usr-ein/TriMixxx/prolinks-compat/research/10-mixxx-prolink-implementation-plan.md

# 10 — Implementation plan: two-way ProLink in Mixxx

The approved build plan for Phase B. Supersedes the sketch in
[08-python-poc-plan.md](08-python-poc-plan.md) and corrects the licensing claims in
[09-mixxx-integration-notes.md](09-mixxx-integration-notes.md).

Grounded in a full read of the Mixxx source at `../mixxx` (fork of 2.5.6). Line
references are to that tree.

**Revised 2026-07-30** for two changes of direction:

1. **Serving is v1 scope, not a later phase.** Phase A proved both directions
   against real hardware, so the old "consume now, serve someday" split has no
   remaining justification. Former Phase C is folded into Phase B.
2. **Kaitai Struct describes the wire formats.** With one large caveat that
   shapes the whole design — see [§Kaitai](#kaitai-struct-what-it-can-and-cannot-do-here).

> Implement from [`docs/PROTOCOL.md`](../docs/PROTOCOL.md), not from this file
> and not from `research/00`–`09`. This document says *how to build it in Mixxx*;
> PROTOCOL.md says *what the bytes are*. Where they disagree, PROTOCOL.md wins.

**Status, 2026-07-31 — the serve side is built and verified on hardware.** Two
CDJ-2000NXS browse and play from sticks in the deck's own USB ports: media query
answered, portmapper and mountd and nfsd bound, dbserver on 1051, both slots
advertised (`/C/` USB and `/B/` SD) with their real labels and counts. Yanking a
stick mid-play stops the playing deck cleanly and clears the slot within ~2 s;
re-inserting restores it to the same slot. What that leaves untested is the
long tail rather than the mechanism: mixers, CDJ-3000s, more than two peers, and
a set's worth of uptime. Findings from the exercise are `F52` onward.

## Working-directory conventions

- `prolinks-compat/` — research docs, the Python PoC (`prolinks_poc/`, `tests/`),
  and the `.ksy` sources. `captures/` and `research/ref-repos/` stay git-ignored.
- `mixxx/` — the C++ fork. No PoC artifacts land there; only `src/`, `res/`,
  `CMakeLists.txt` changes, plus the generated Kaitai output.
- Commit straight to `main` in both repos — no PRs (standing convention for this
  project). Upstreaming to mixxxdj/mixxx is a separate, later exercise; see
  [§Upstreaming](#upstreaming-reality-check).

---

## Target behaviour

The feature as specified, in the order a user meets it.

### On boot

- If **enabled in Mixxx settings** (default off), Mixxx acts as a CDJ on the
  Pro DJ Link network. Disabled, it transmits nothing and binds nothing.
- It advertises a **given player number, or AUTO** — AUTO is the default.
- It watches the filesystem for mounted volumes carrying a rekordbox database,
  and **reports media inserted/ejected** to other players as it sees them appear
  and disappear.

### Serving

- Other CDJs **browse the media mounted in Mixxx** — the same categories, sorts,
  drill-downs and search a real CDJ offers — and load and play tracks from them.
- **Only the first two volumes** are served: the first fills the **USB** slot,
  the second the **SD** slot. A third is ignored.
- **The internal Mixxx library is never shared.** Only rekordbox media are.

### Consuming

- Mixxx finds other CDJs on the network and lists them in the library sidebar
  under **ProLink**:

  ```
  ProLink
  ├─ 1 · CDJ-2000nexus
  │  ├─ USB
  │  └─ SD
  └─ 2 · CDJ-2000nexus  (offline)
  ```

- Opening a slot **downloads and parses that medium's `export.pdb`** over NFS.
- Loading a track **downloads the whole file into a local cache**, which is
  **cleared at every boot**.

> **Reading of "menu bar".** The requirement says CDJs "display in the menu bar
> under ProLink", with the path `ProLink > 1 - CDJ 2000 Nxs > USB/SD`. A
> three-level browsable, track-loadable hierarchy is the library sidebar, not
> Qt's menu bar — Mixxx has no other surface that can do this. Built as a
> `LibraryFeature`.
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
