usr-ein/TriMixxx/boards/one_button/v1_layout.png

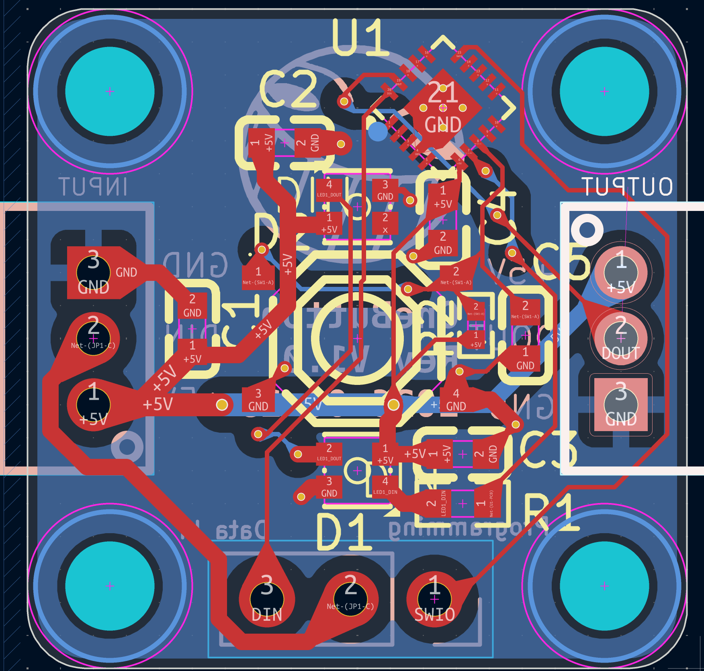
boards/one_button/v1_layout.png
