usr-ein/TriMixxx/handmade_pcb/export_kicad10_b_cu.png

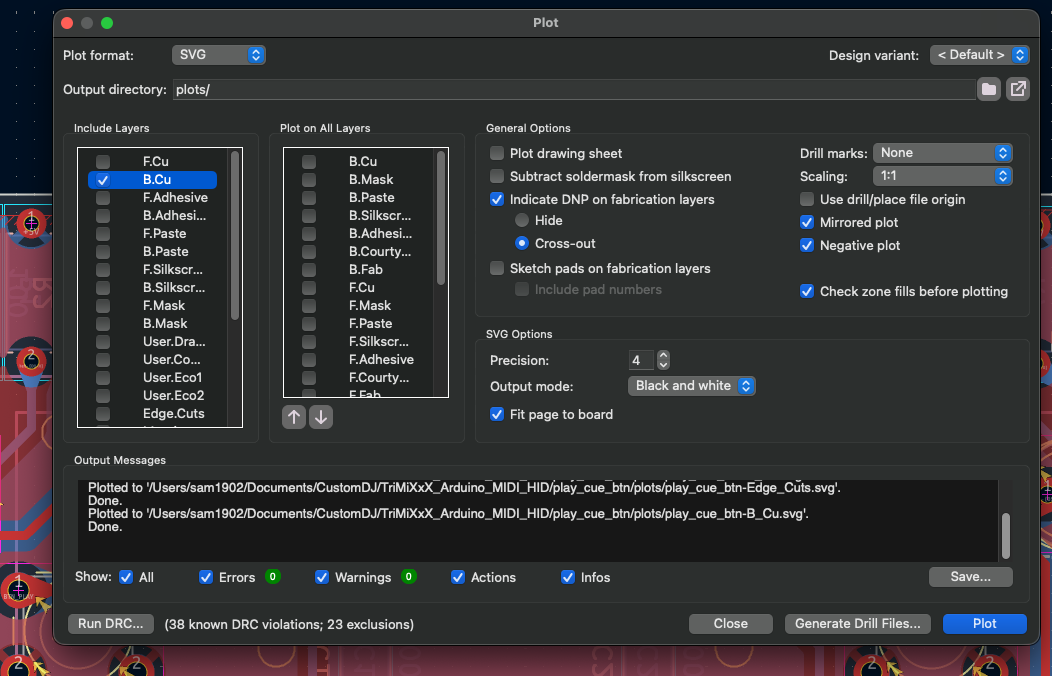
handmade_pcb/export_kicad10_b_cu.png
