usr-ein/TriMixxx/ref_sizes/cdj1000mk3_top_case_skwik.png

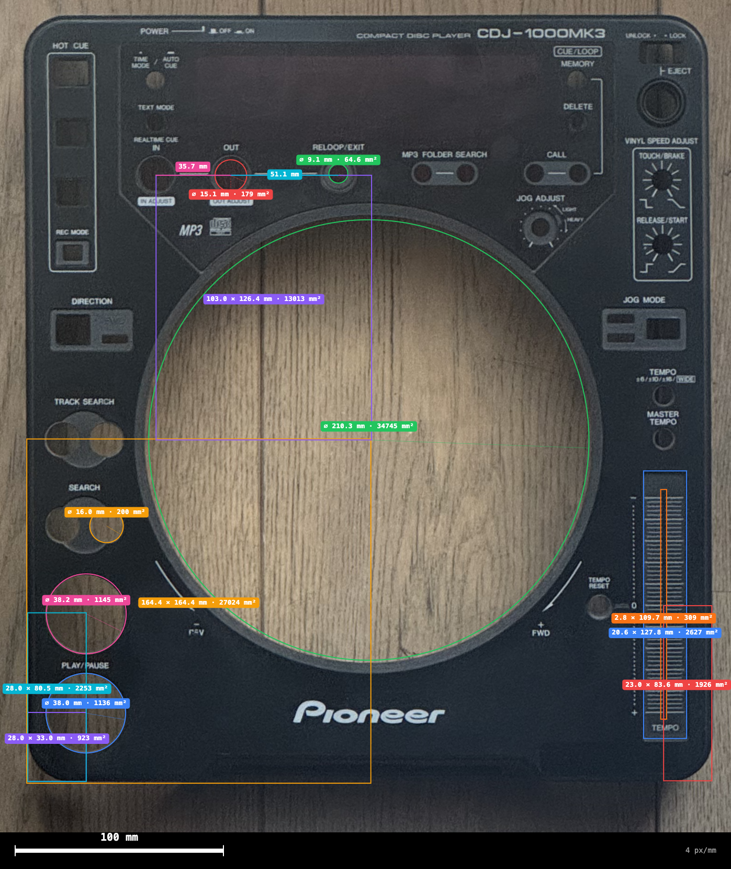
ref_sizes/cdj1000mk3_top_case_skwik.png
