usr-ein/TriMixxx/ref_sizes/cdj2000nx2-skwik.png

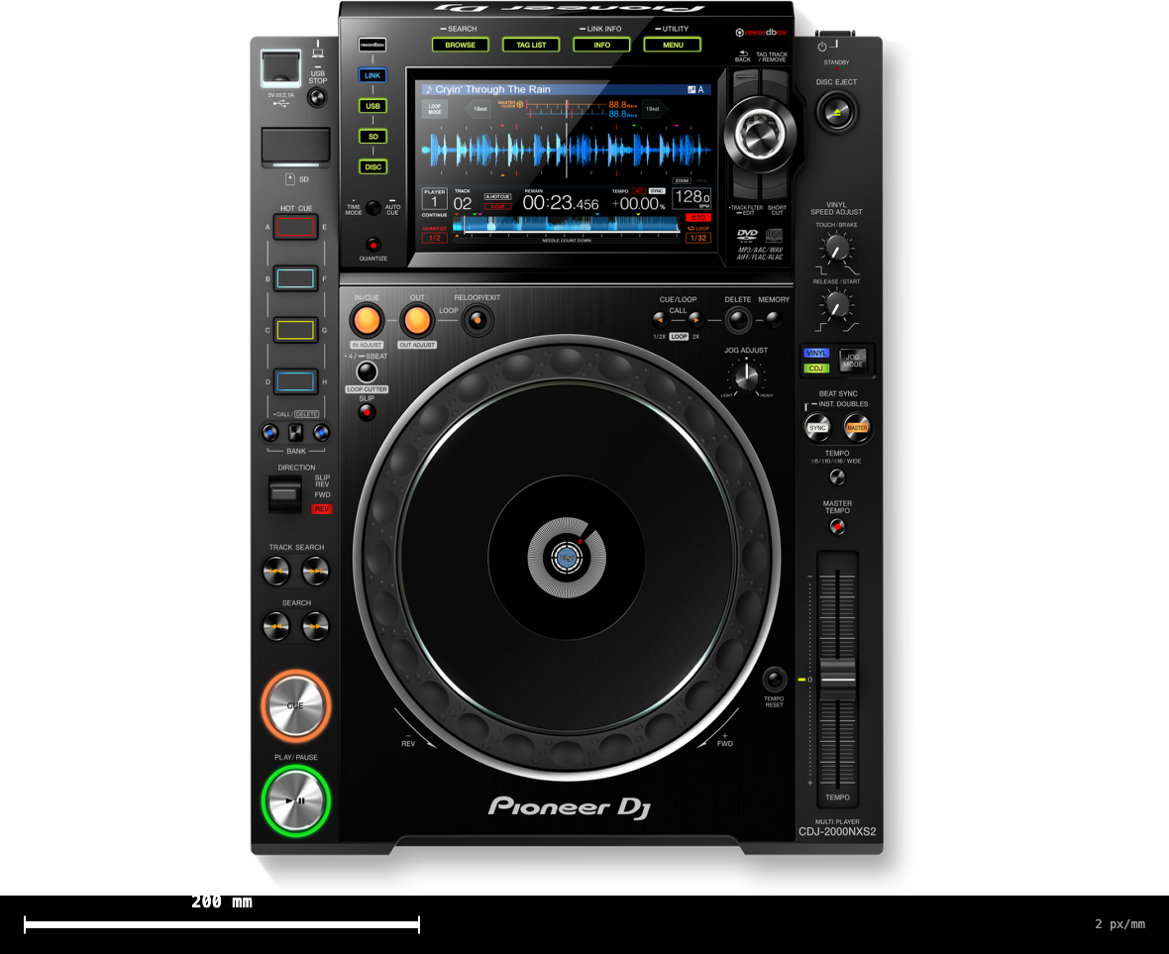
ref_sizes/cdj2000nx2-skwik.png
