usr-ein/TriMixxx/ref_sizes/cdj2000nx2.png

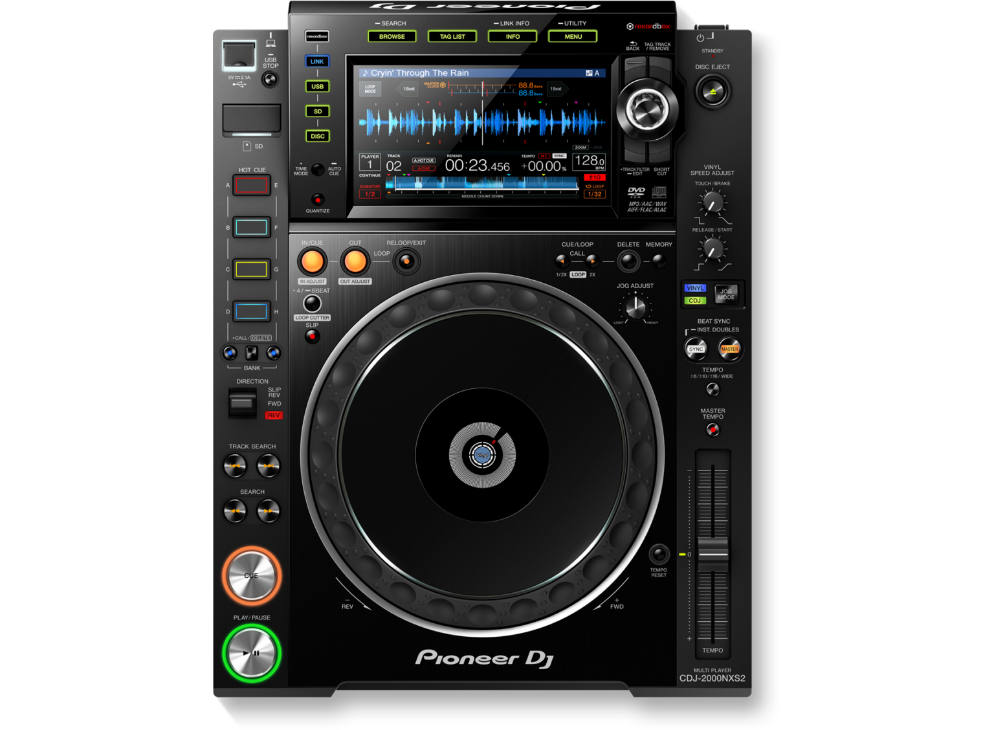
ref_sizes/cdj2000nx2.png
