usr-ein/TriMixxx/ref_sizes/cdj3000-skwik.png

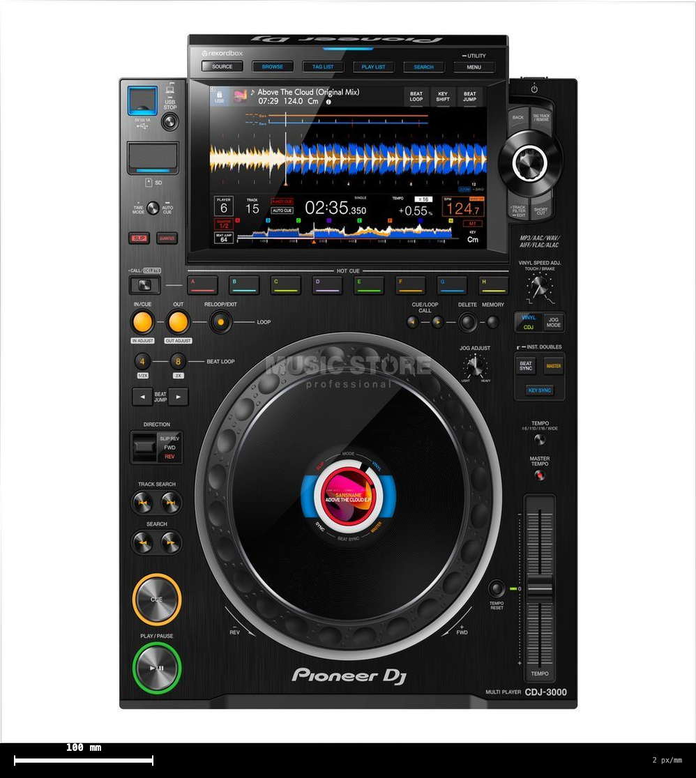
ref_sizes/cdj3000-skwik.png
