usr-ein/TriMixxx/ref_sizes/CDJ-3000_top.png

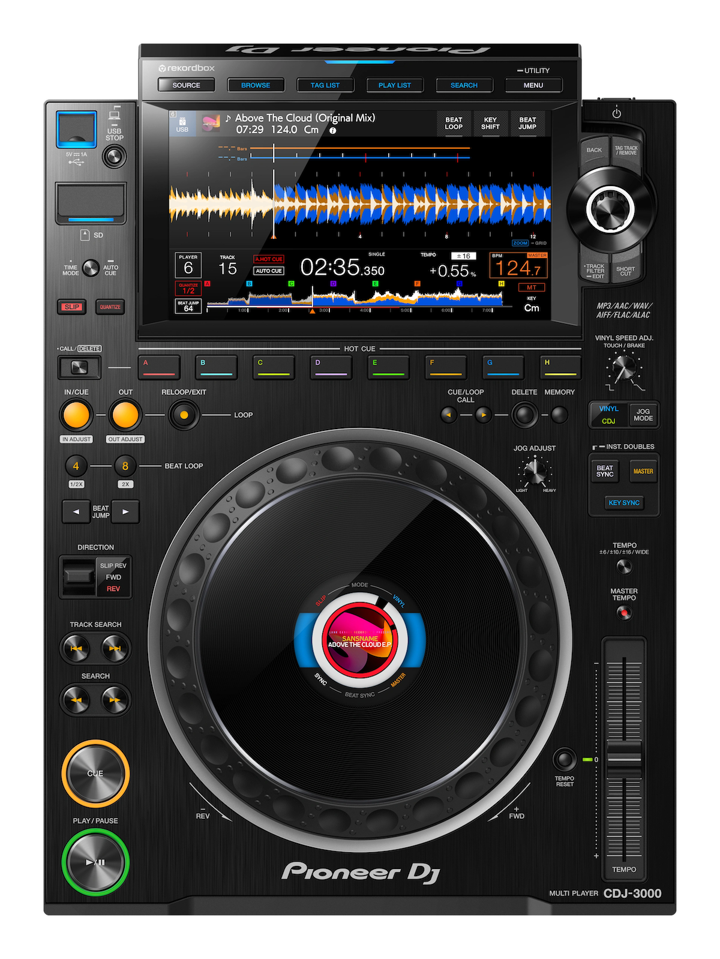
ref_sizes/CDJ-3000_top.png
