usr-ein/TriMixxx/ref_sizes/mixxx.png

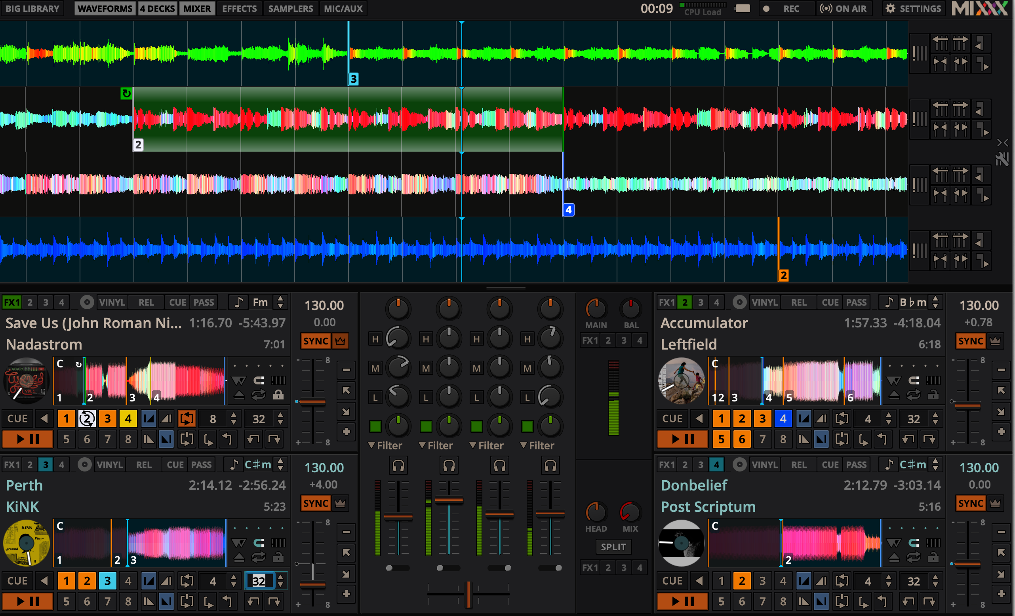
ref_sizes/mixxx.png
