usr-ein/TriMixxx/ref_sizes/scr_image.png

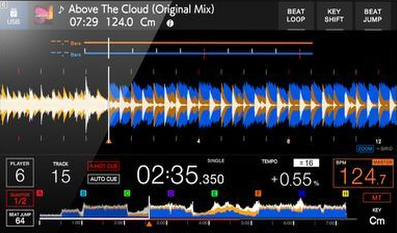
ref_sizes/scr_image.png
