usr-ein/TriMixxx/screenshots/audio_2026-02-17.png

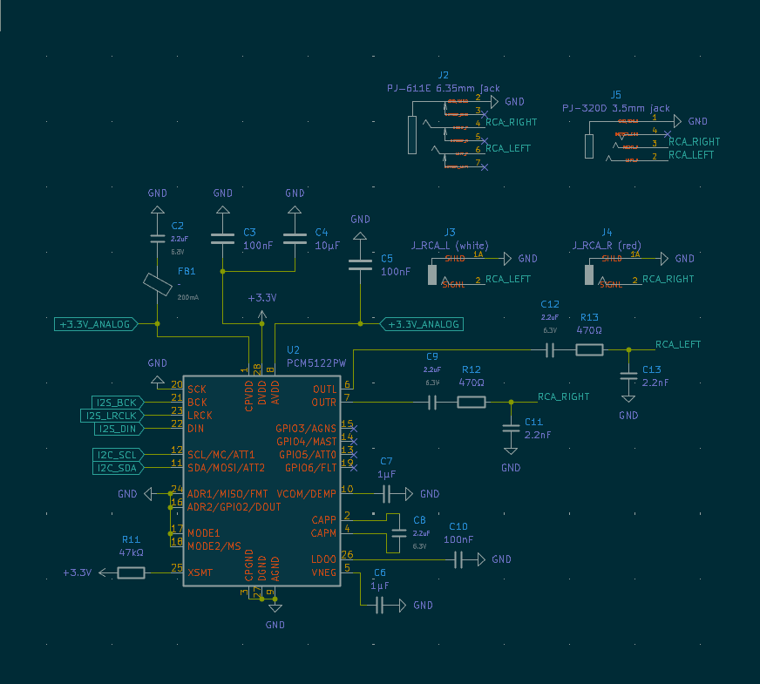
screenshots/audio_2026-02-17.png
