usr-ein/TriMixxx/screenshots/CDJ-MainBoard-v1_fully_routed.png

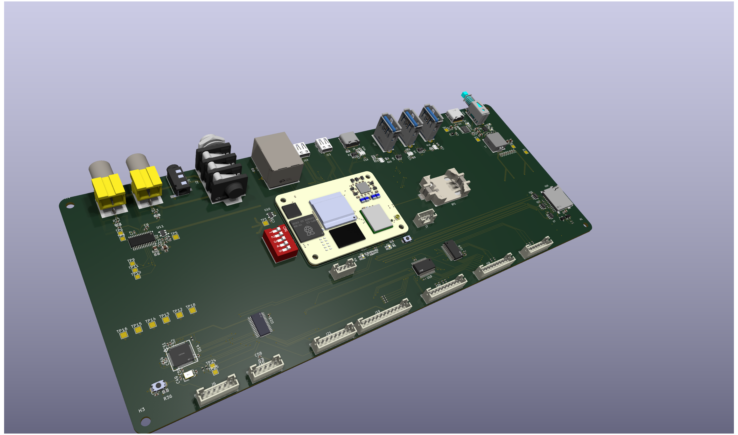
screenshots/CDJ-MainBoard-v1_fully_routed.png
