usr-ein/TriMixxx/screenshots/CDJ-TriMixxx-master-doc_v117_back.png

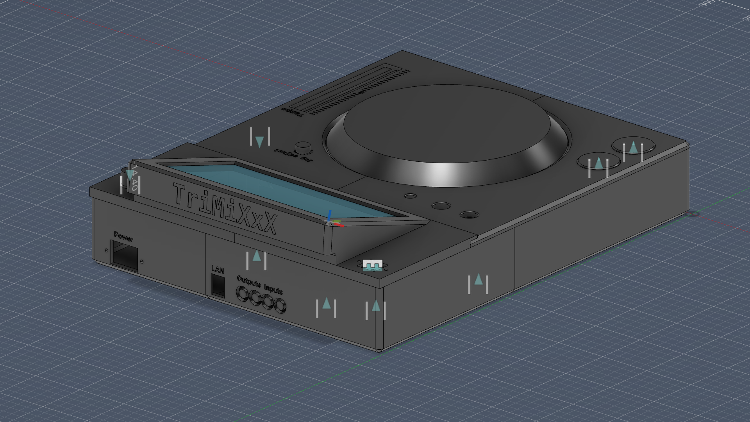
screenshots/CDJ-TriMixxx-master-doc_v117_back.png
