usr-ein/TriMixxx/screenshots/CDJ-TriMixxx-master-doc_v117_front.png

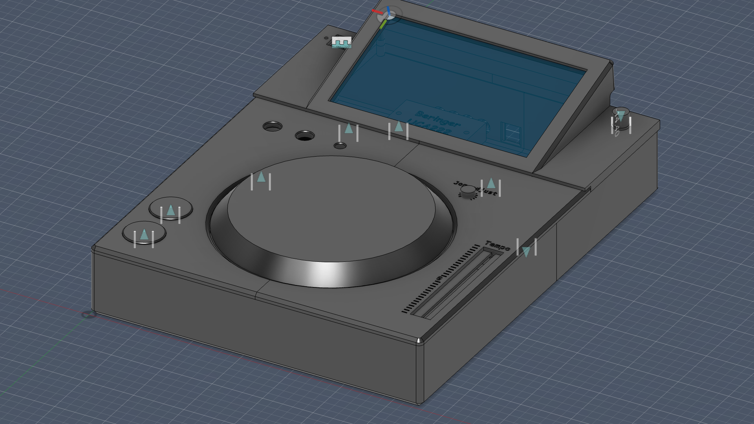
screenshots/CDJ-TriMixxx-master-doc_v117_front.png
