usr-ein/TriMixxx/screenshots/dac_spice.png

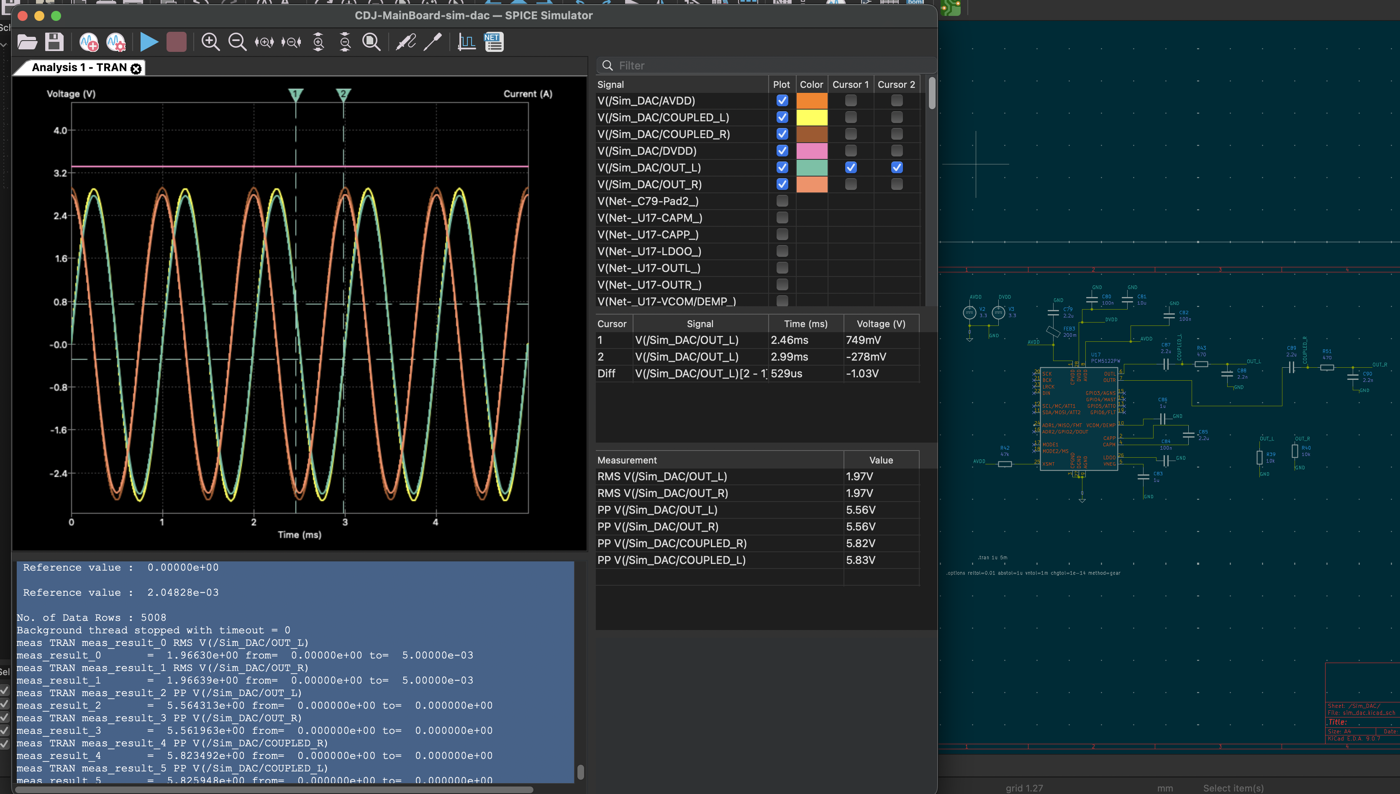
screenshots/dac_spice.png
