usr-ein/TriMixxx/screenshots/midi_arduino_2026-02-17.png

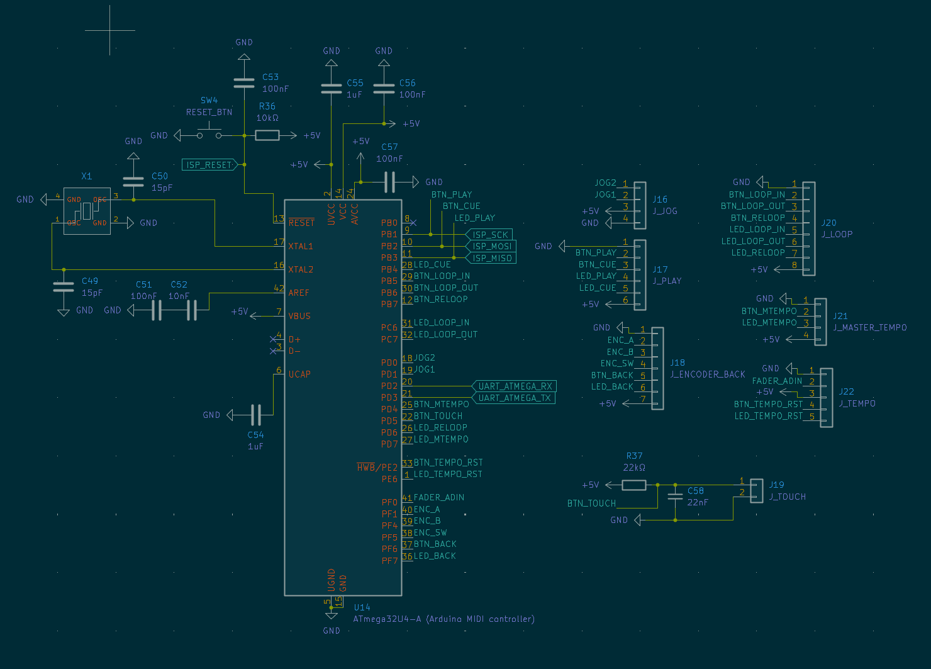
screenshots/midi_arduino_2026-02-17.png
