usr-ein/TriMixxx/screenshots/pcb-3d-render.png

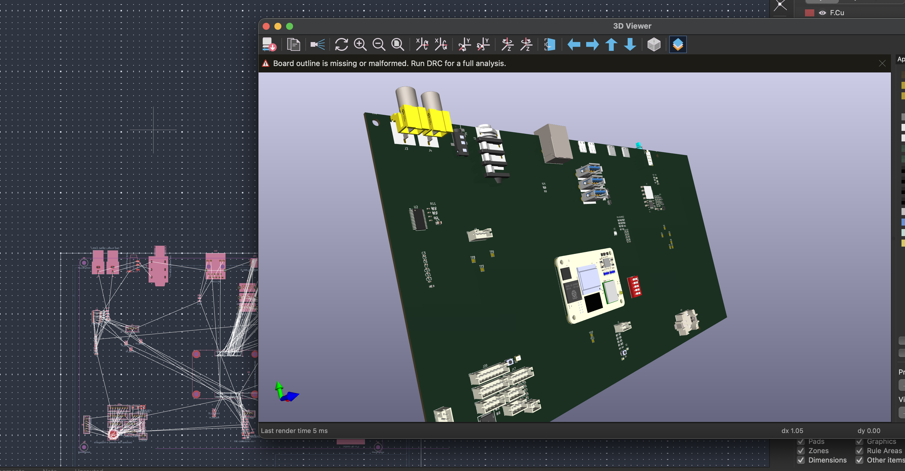
screenshots/pcb-3d-render.png
