usr-ein/TriMixxx/screenshots/power_delivery_2026-02-17.png

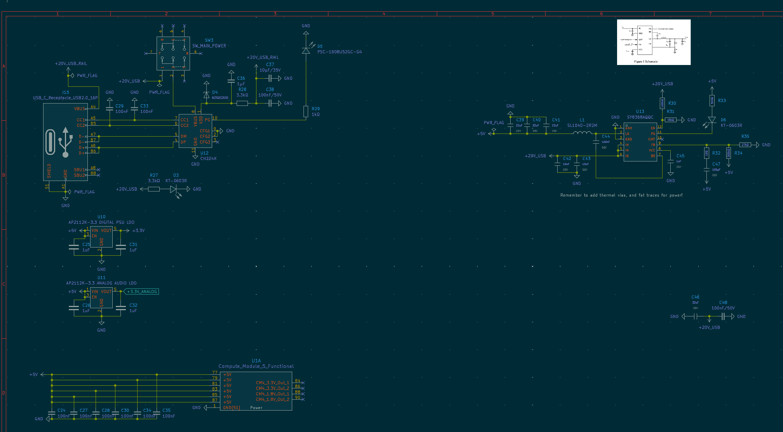
screenshots/power_delivery_2026-02-17.png
