usr-ein/TriMixxx/screenshots/Screenshot 2026-02-08 at 19.56.48.png

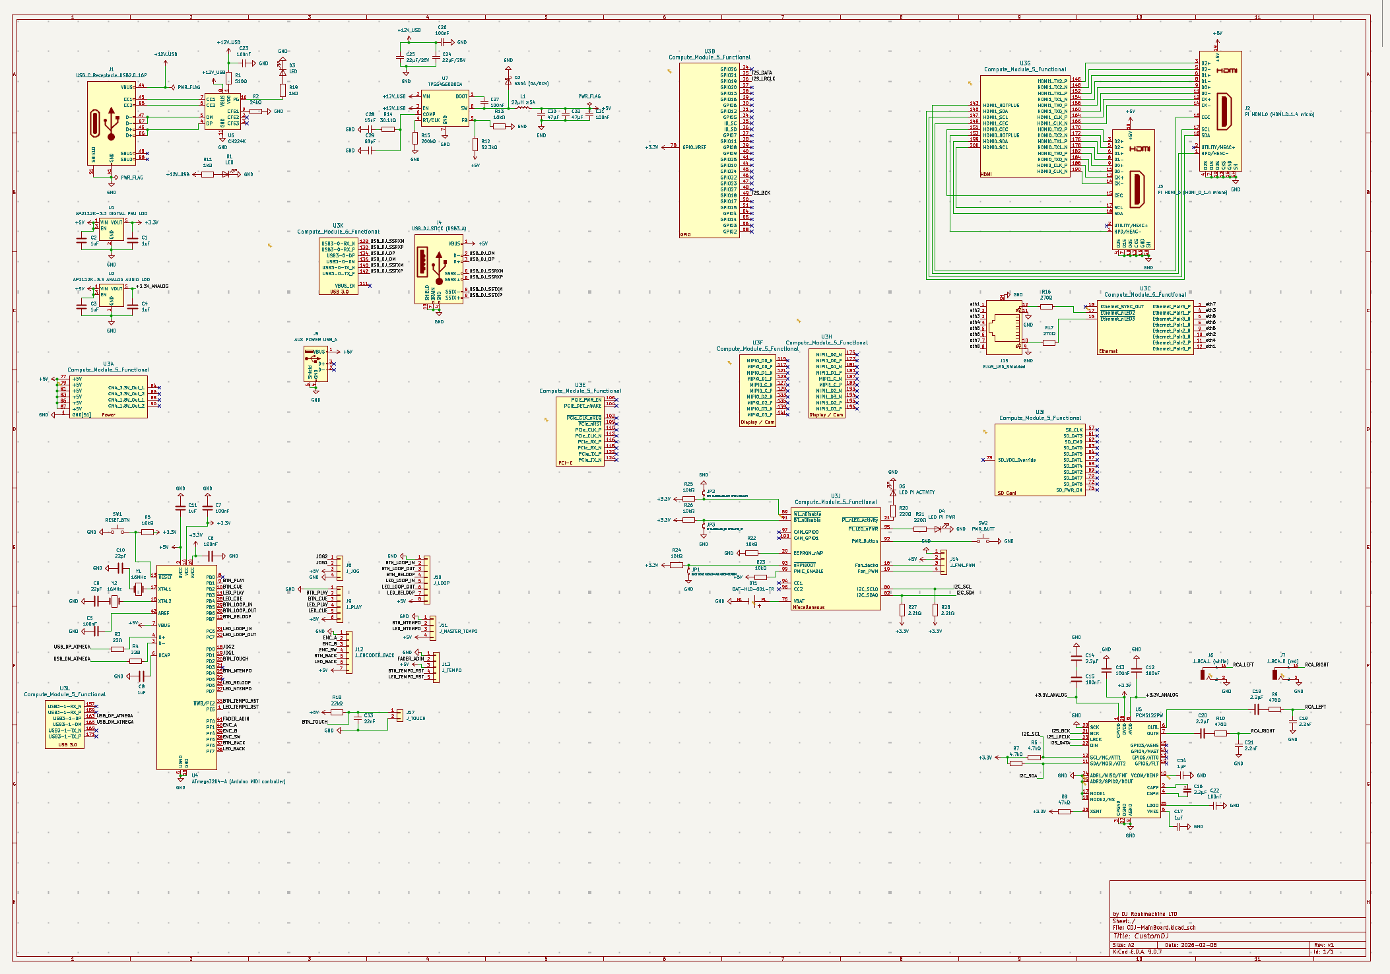
screenshots/Screenshot 2026-02-08 at 19.56.48.png
