usr-ein/TriMixxx/screenshots/usb_2026-02-17.png

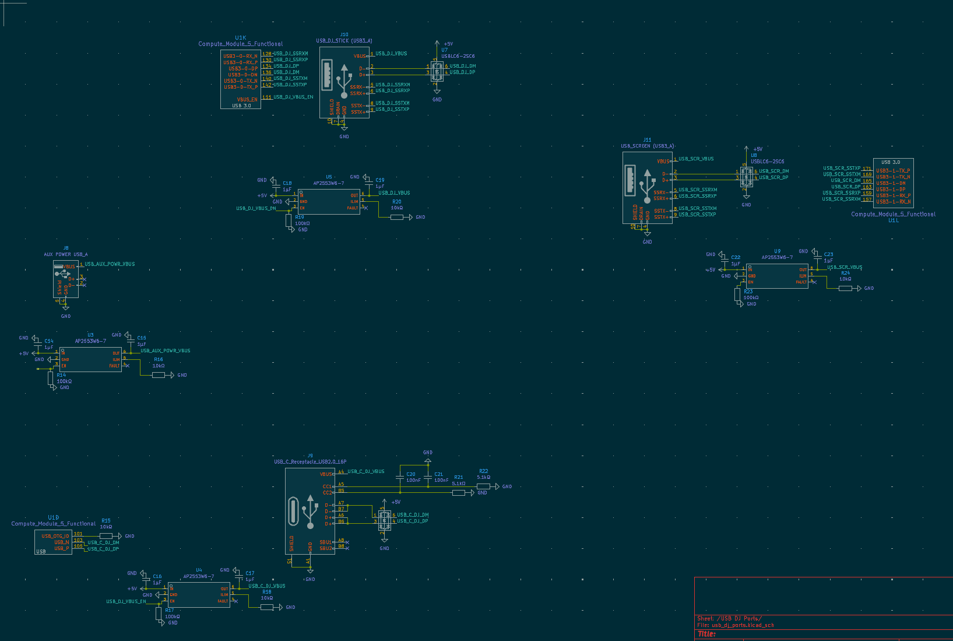
screenshots/usb_2026-02-17.png
