usr-ein/TriMixxx/ref_sizes/IMG_8324-measured-view.png

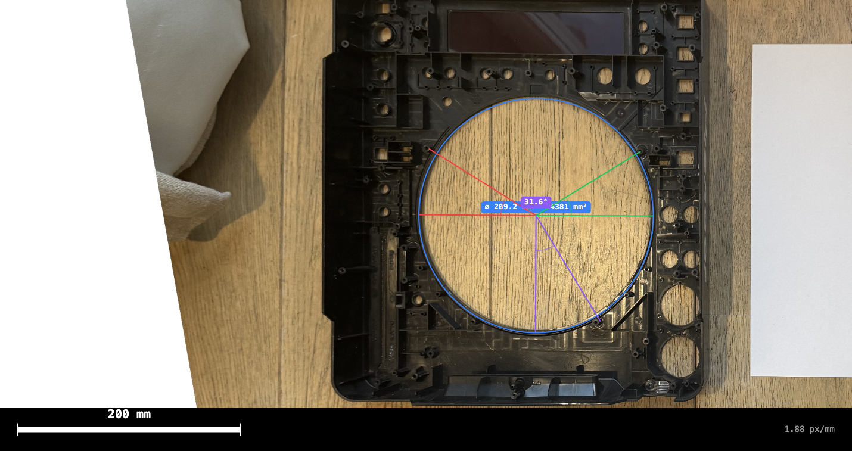
ref_sizes/IMG_8324-measured-view.png
