usr-ein/TriMixxx/ref_sizes/jog_front-measured.png

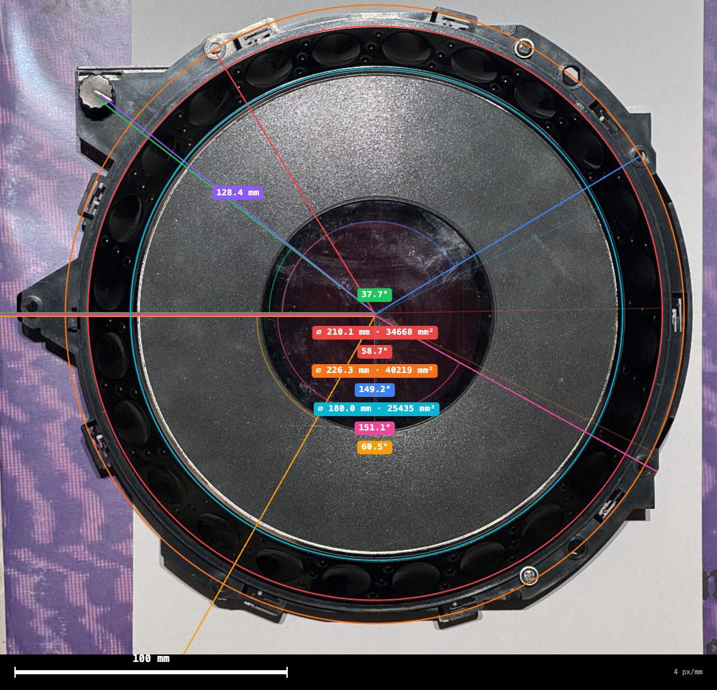
ref_sizes/jog_front-measured.png
