usr-ein/TriMixxx/ref_sizes/jog_side_2-measured.png

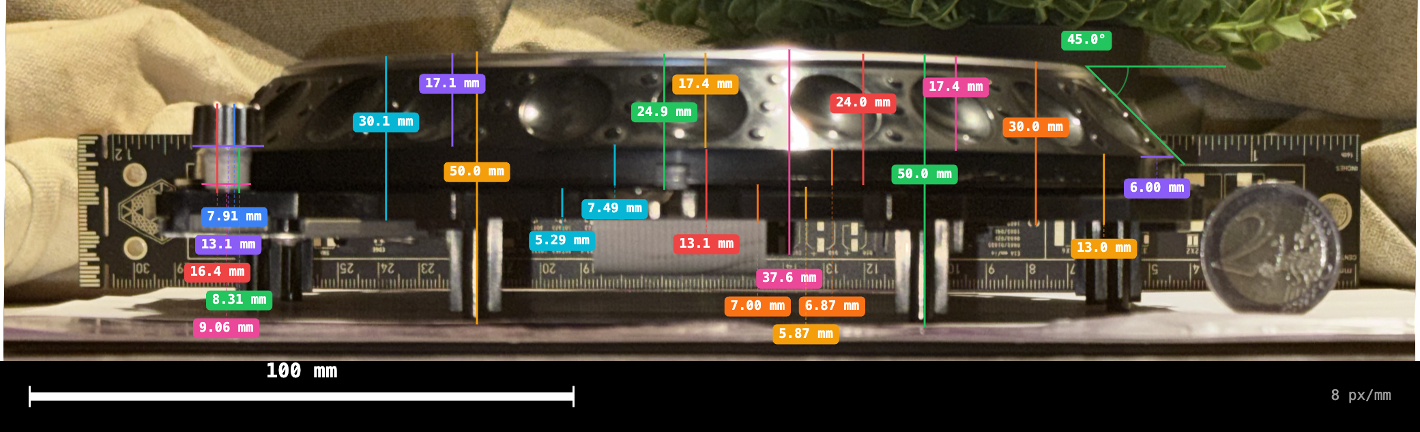
ref_sizes/jog_side_2-measured.png
