usr-ein/TriMixxx/ref_sizes/screen.raw-measured.png

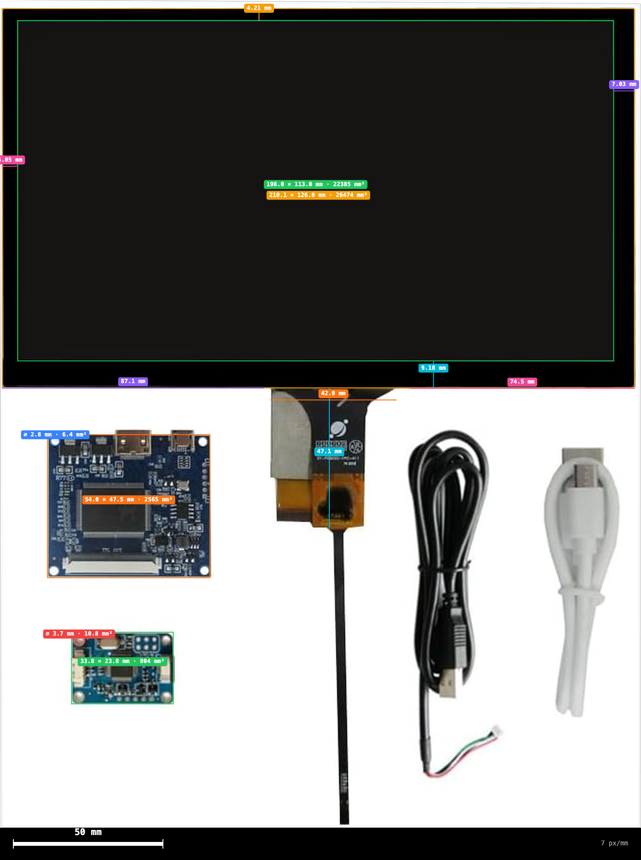
ref_sizes/screen.raw-measured.png
