usr-ein/TriMixxx/pi-qemu/app/src/s3/protocol.cpp

#include "s3/protocol.h"

#include "MidiMap.hpp"

using namespace midimap;

namespace s3 {

QByteArray button(quint8 note, bool down) {
    // One pair per press, nothing while held (btnToNote in main.cpp).
    QByteArray b;
    b += char((down ? 0x90 : 0x80) | CHANNEL);
    b += char(note & 0x7F);
    b += char(down ? 127 : 0);
    return b;
}

QByteArray jog(int ticks) {
    QByteArray out;
    while (ticks) {
        const int chunk = qBound(-63, ticks, 63);
        out += char(0xB0 | CHANNEL);
        out += char(CC_JOG);
        out += char(chunk & 0x7F);
        ticks -= chunk;
    }
    return out;
}

QByteArray encoder(int detents) {
    QByteArray b;
    for (int i = 0; i < qAbs(detents); i++) {
        b += char(0xB0 | CHANNEL);
        b += char(CC_ENCODER);
        b += char(detents > 0 ? 1 : 127);
    }
    return b;
}

QByteArray tempo(int v) {
    v = qBound(0, v, 16383);
    QByteArray b;
    b += char(0xB0 | CHANNEL); b += char(CC_TEMPO);     b += char(v >> 7);
    b += char(0xB0 | CHANNEL); b += char(CC_TEMPO_LSB); b += char(v & 0x7F);
    return b;
}

bool parseHex(const QStringList& words, QByteArray* out) {
    out->clear();
    for (const QString& w : words) {
        bool ok = false;
        const uint v = w.toUInt(&ok, 16);
        if (!ok || v > 0xFF) return false;
        *out += char(v);
    }
    return !out->isEmpty();
}

void Feedback::feed(const QByteArray& in) {
    for (char c : in) {
        const quint8 b = quint8(c);
        if (b & 0x80) {
            if (b >= 0xF8) continue; // real-time: anywhere, ignored, state untouched
            if (m_inSysEx) {
                m_inSysEx = false;
                if (b == 0xF7) { sysex(m_sysex); continue; }
            }
            if (b == 0xF0) { m_inSysEx = true; m_sysex.clear(); m_status = 0; continue; }
            if (b >= 0xF0) { m_status = 0; continue; }
            m_status = b;
            const quint8 hi = b & 0xF0;
            m_needed = (hi == 0xC0 || hi == 0xD0) ? 1 : 2;
            m_count = 0;
            continue;
        }
        if (m_inSysEx) {
            if (m_sysex.size() < 64) m_sysex += char(b); // longer: dropped whole at F7
            else m_sysex += char(0x80);                  // poison: never a valid payload
            continue;
        }
        if (!m_status) continue;
        if (m_count == 0) {
            m_d1 = b;
            m_count = 1;
            if (m_needed == 1) { message(m_status, m_d1, 0); m_count = 0; }
            continue;
        }
        message(m_status, m_d1, b);
        m_count = 0;
    }
}

void Feedback::message(quint8 status, quint8 d1, quint8 d2) {
    const quint8 type = status & 0xF0;
    // Note-On velocity on a ring pad = white brightness, LED0 only, on the
    // LEDs' 0..255 scale as main.cpp passes it (so at most half brightness).
    if (type == 0x90 && d1 < PAD_A_BASE + PAD_A_COUNT) {
        m_leds.ringA[d1 - PAD_A_BASE][0] = QColor(d2, d2, d2);
    } else if (type == 0x90 && d1 >= PAD_B_BASE && d1 < PAD_B_BASE + PAD_B_COUNT) {
        m_leds.ringB[d1 - PAD_B_BASE][0] = QColor(d2, d2, d2);
    } else if (type == 0x90 || type == 0x80) {
        const bool on = type == 0x90 && d2 > 0;
        switch (d1) {
        case NOTE_PLAY: m_leds.play = on; break;
        case NOTE_CUE: m_leds.cue = on; break;
        case NOTE_LOOP_IN: m_leds.loopIn = on; break;
        case NOTE_LOOP_OUT: m_leds.loopOut = on; break;
        default: return; // RELOOP has no LED
        }
    } else {
        return;
    }
    if (onLeds) onLeds();
}

void Feedback::sysex(const QByteArray& p) {
    if (p.size() < 2 || quint8(p[0]) != SYSEX_MFR_ID || p.contains(char(0x80))) return;
    const quint8 cmd = quint8(p[1]);
    const QByteArray args = p.mid(2);
    auto nib = [&](int i) { return (quint8(args[i]) << 4) | (quint8(args[i + 1]) & 0x0F); };
    if (cmd == SYSEX_CMD_RING_LED || cmd == SYSEX_CMD_RING_B_LED) {
        const int n = args.size();
        if (n != SYSEX_RING_LED_ARGS_ONE && n != SYSEX_RING_LED_ARGS_TWO) return;
        const int node = quint8(args[0]);
        if (node >= 50) return;
        auto& ring = cmd == SYSEX_CMD_RING_LED ? m_leds.ringA : m_leds.ringB;
        ring[node][0] = QColor(nib(1), nib(3), nib(5));
        ring[node][1] = n == SYSEX_RING_LED_ARGS_ONE ? ring[node][0] : QColor(nib(7), nib(9), nib(11));
        if (onLeds) onLeds();
    } else if (cmd == SYSEX_CMD_RESET && args == QByteArray("RST")) {
        m_leds = DeckLeds{};
        if (onLeds) onLeds();
        if (onReboot) onReboot();
    }
}

} // namespace s3
