usr-ein/TriMixxx/firmwares/onebutton/onebutton_node/funconfig.h

#ifndef _FUNCONFIG_H
#define _FUNCONFIG_H

// Place configuration items here, you can see a full list in ch32fun/ch32fun.h
// To reconfigure to a different processor, update TARGET_MCU in the Makefile.

#endif
